giodestone/Hart-Keyboard/Images/Image1.PNG

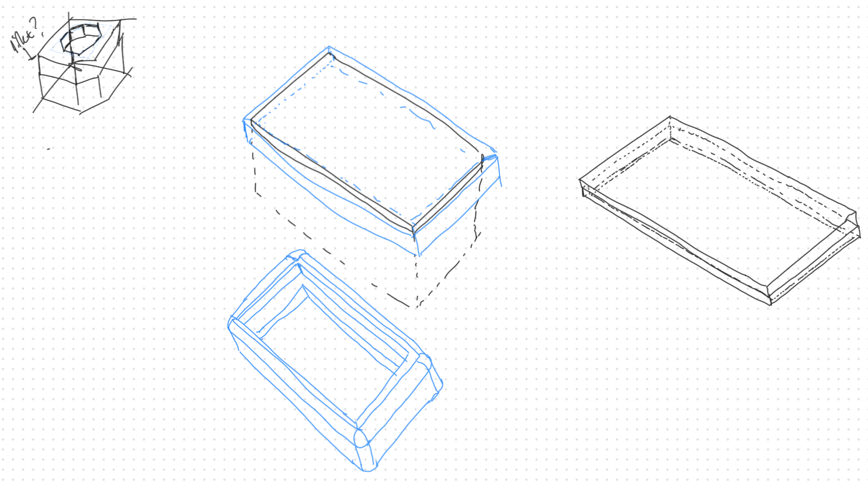
Images/Image1.PNG
